MiLasGeek/SVA-Fencing-Tester-Portal/docs/assets/hist_01_breadboard_2024.png

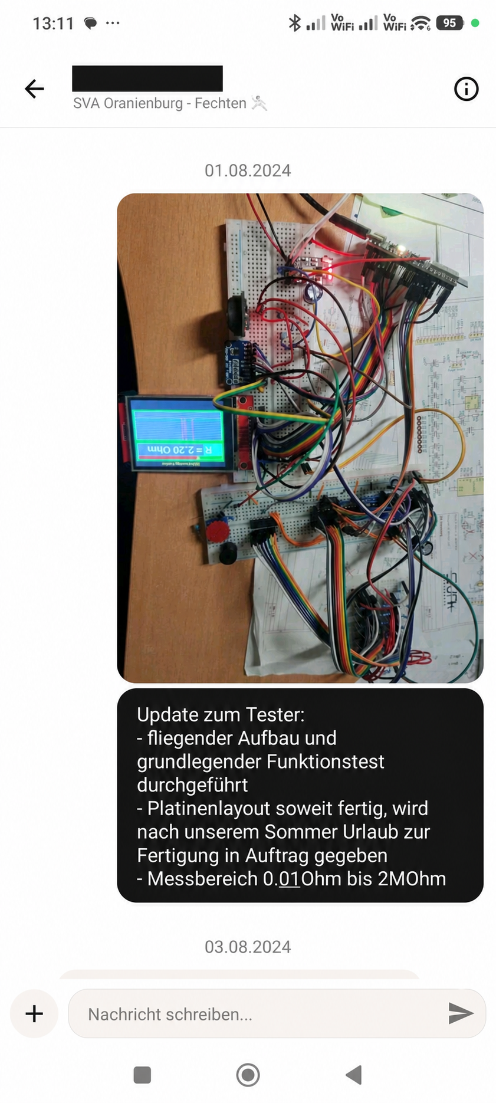
docs/assets/hist_01_breadboard_2024.png
