MiLasGeek/SVA-Fencing-Tester-Portal/docs/manuals/assets/manual_de/manual-de-10.jpeg

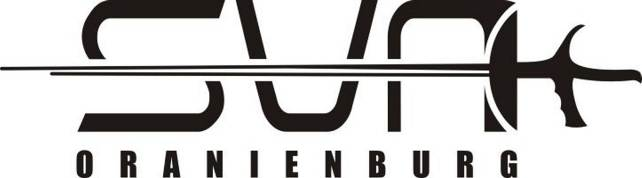
docs/manuals/assets/manual_de/manual-de-10.jpeg
